spider-tronix/MU_CON_2019/Design/assembly-files/Header_Female_1x6.SLDPRT

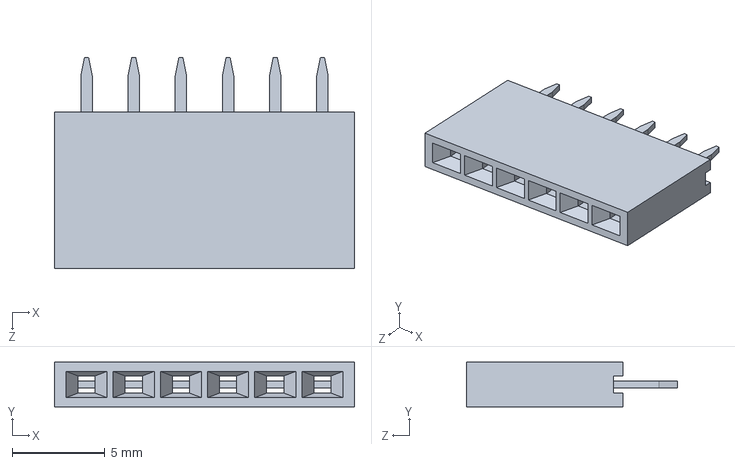
[picture p19: CAD file, 2019-09-01]
Design/assembly-files/Header_Female_1x6.SLDPRT
16.1 x 2.42 x 11.4 mm
