spider-tronix/MU_CON_2019/Design/assembly-files/SG90 - Micro Servo 9g - Tower Pro.2.SLDPRT

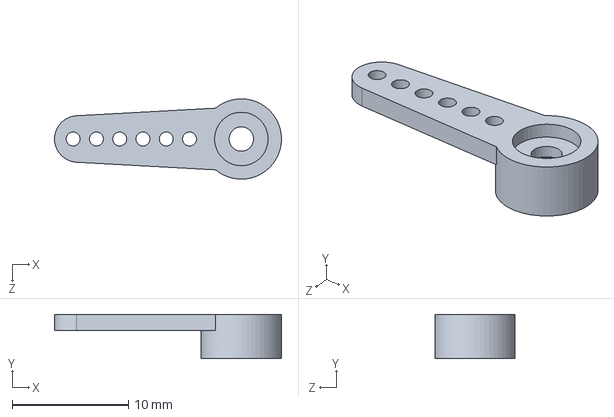
[picture p20: CAD file, 2019-09-01]
Design/assembly-files/SG90 - Micro Servo 9g - Tower Pro.2.SLDPRT
19.5 x 3.80 x 6.90 mm
