spider-tronix/MU_CON_2019/Design/assembly-files/Header_Female_1x2.SLDPRT

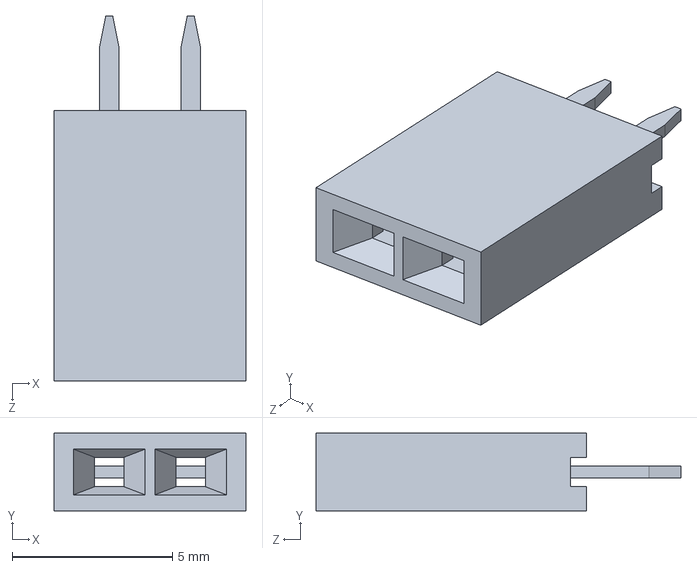
[picture p21: CAD file, 2019-09-01]
Design/assembly-files/Header_Female_1x2.SLDPRT
5.99 x 2.42 x 11.4 mm
