spider-tronix/MU_CON_2019/Design/assembly-files/rsw.SLDPRT

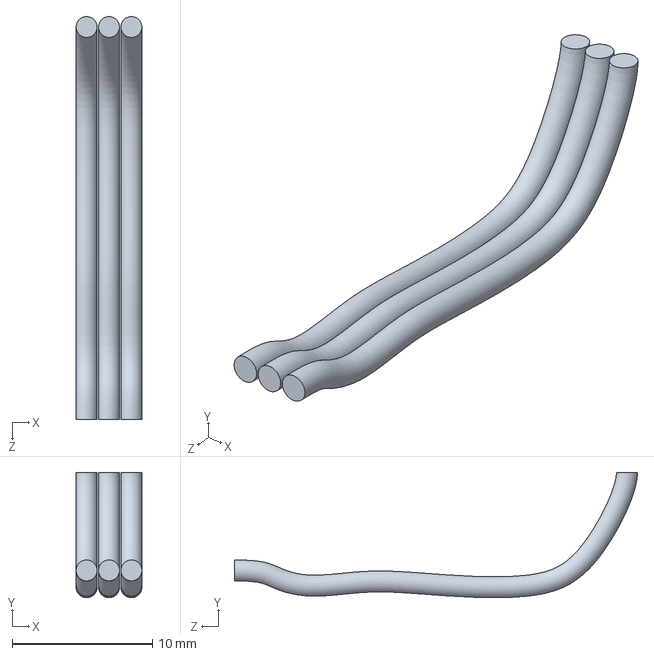
[picture p22: CAD file, 2019-09-01]
Design/assembly-files/rsw.SLDPRT
4.70 x 8.95 x 28.8 mm
