spider-tronix/MU_CON_2019/Design/assembly-files/mid-servo-wire.SLDPRT

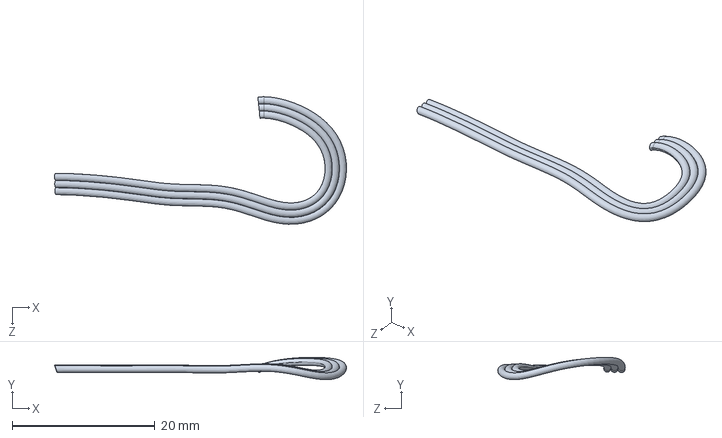
[picture p23: CAD file, 2019-09-01]
Design/assembly-files/mid-servo-wire.SLDPRT
40.9 x 3.12 x 17.9 mm
