spider-tronix/MU_CON_2019/Design/assembly-files/support.SLDPRT

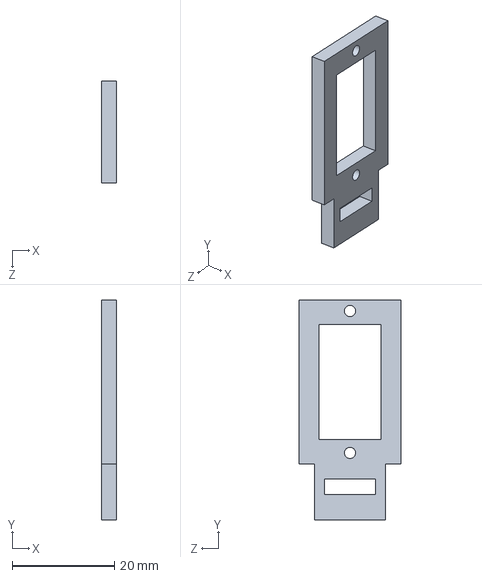
[picture p24: CAD file, 2019-08-31]
Design/assembly-files/support.SLDPRT
3.00 x 43.1 x 20.0 mm
