spider-tronix/MU_CON_2019/Design/assembly-files/support-key.SLDPRT

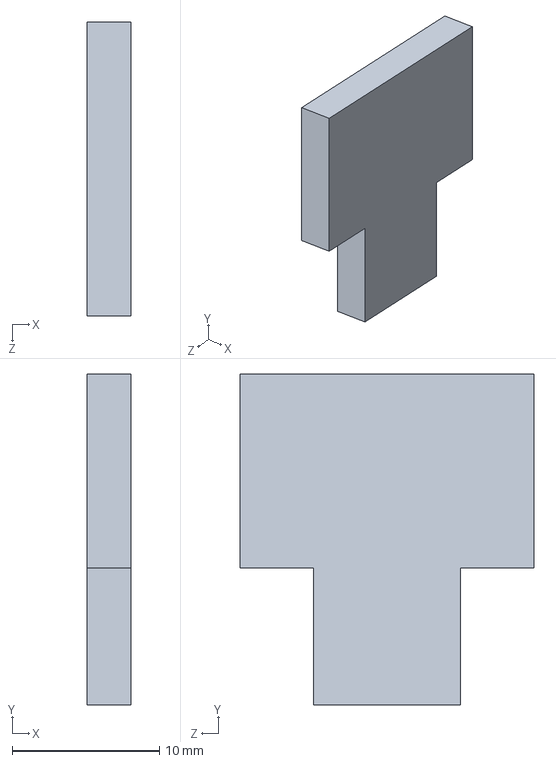
[picture p25: CAD file, 2019-08-31]
Design/assembly-files/support-key.SLDPRT
3.00 x 22.5 x 20.0 mm
